jacob-jarick/esp-solar-contoller/docs/Solar Controller - Day Load.png

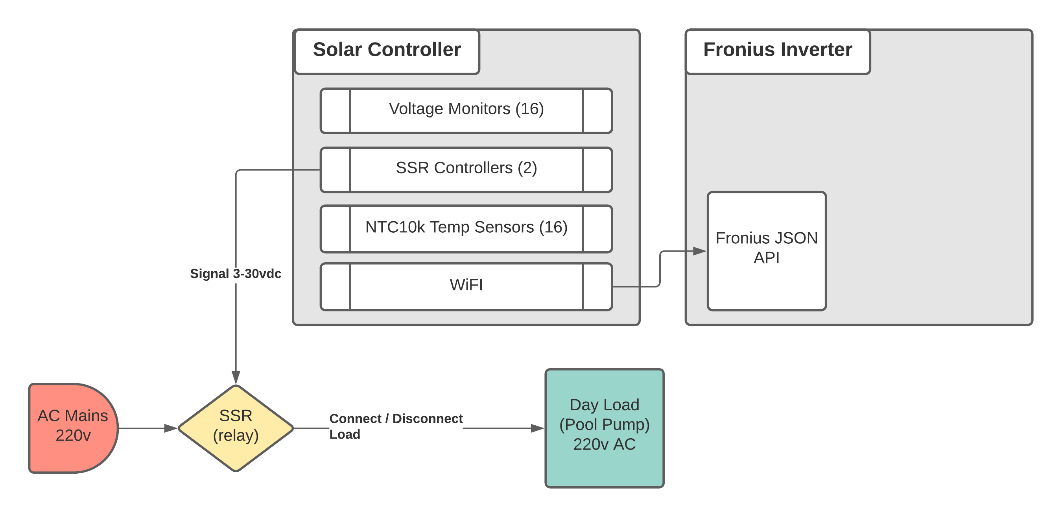
docs/Solar Controller - Day Load.png
