jacob-jarick/esp-solar-contoller/docs/Solar Controller - PowerWall.png

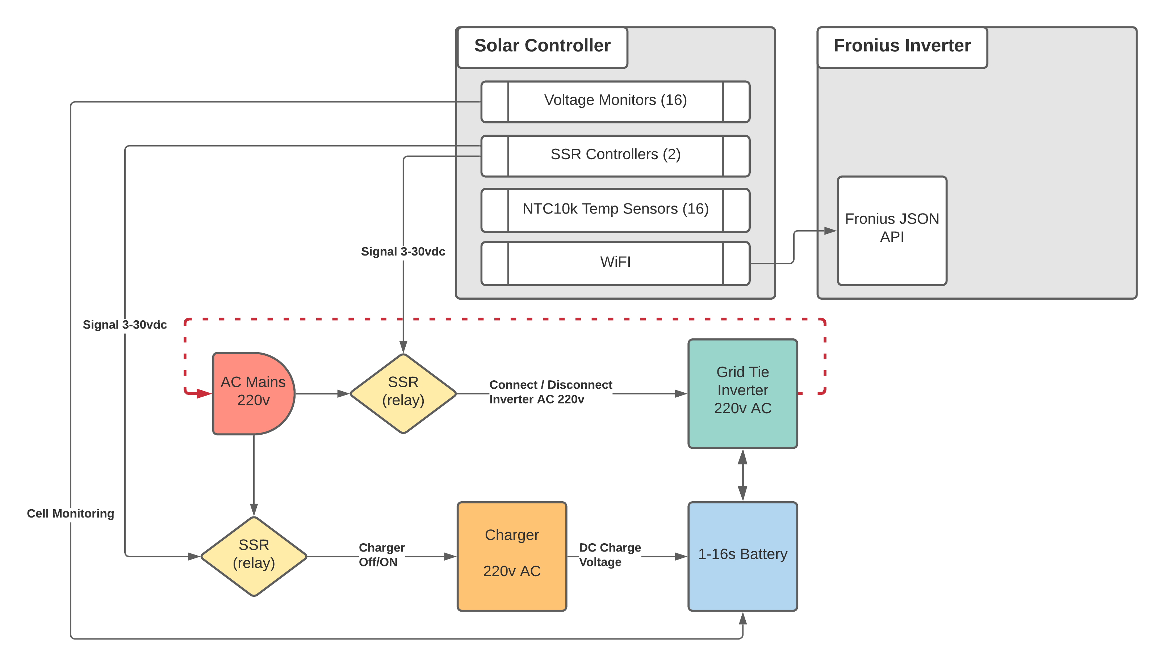
docs/Solar Controller - PowerWall.png
