jacob-jarick/esp-solar-contoller/pictures/advance menu.PNG

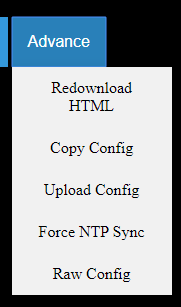
pictures/advance menu.PNG
