jacob-jarick/esp-solar-contoller/pictures/battery config.PNG

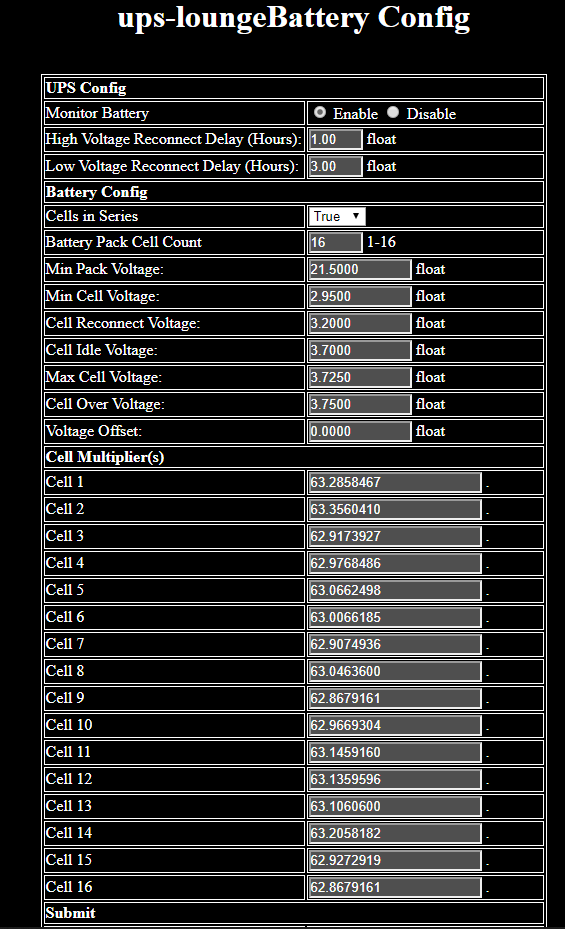
pictures/battery config.PNG
