jacob-jarick/esp-solar-contoller/pictures/battery info.PNG

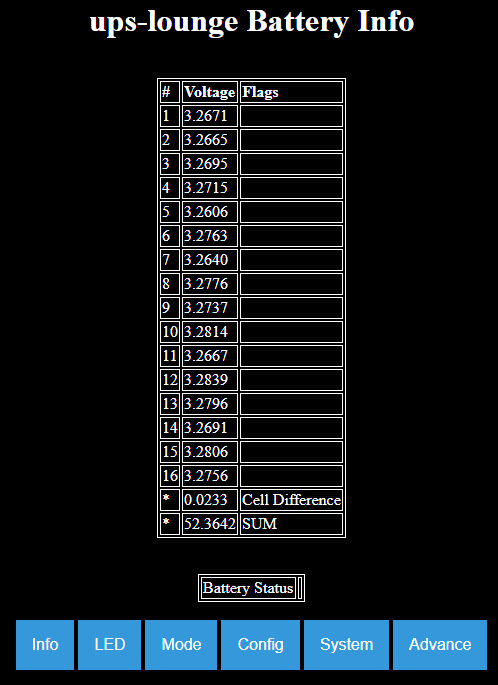
pictures/battery info.PNG
