jacob-jarick/esp-solar-contoller/pictures/config menu.PNG

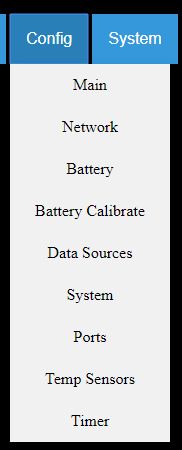
pictures/config menu.PNG
