jacob-jarick/esp-solar-contoller/pictures/info menu.PNG

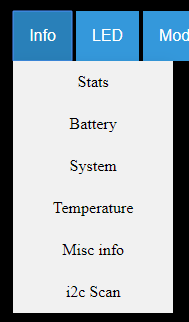
pictures/info menu.PNG
