jacob-jarick/esp-solar-contoller/pictures/led menu.PNG

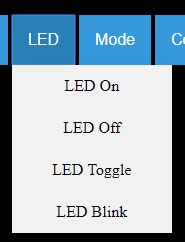
pictures/led menu.PNG
