jacob-jarick/esp-solar-contoller/pictures/main config.PNG

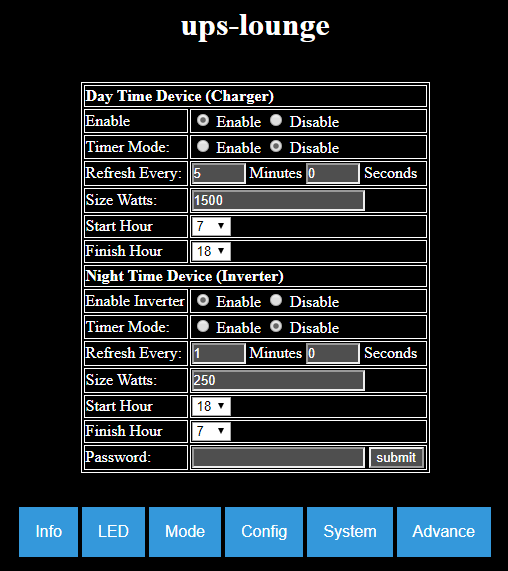
pictures/main config.PNG
