jacob-jarick/esp-solar-contoller/pictures/mode menu.PNG

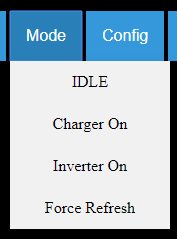
pictures/mode menu.PNG
