jacob-jarick/esp-solar-contoller/pictures/network config.PNG

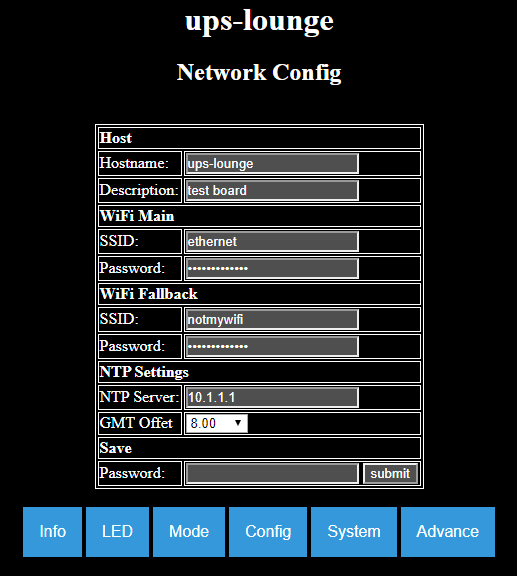
pictures/network config.PNG
