jacob-jarick/esp-solar-contoller/pictures/port config.PNG

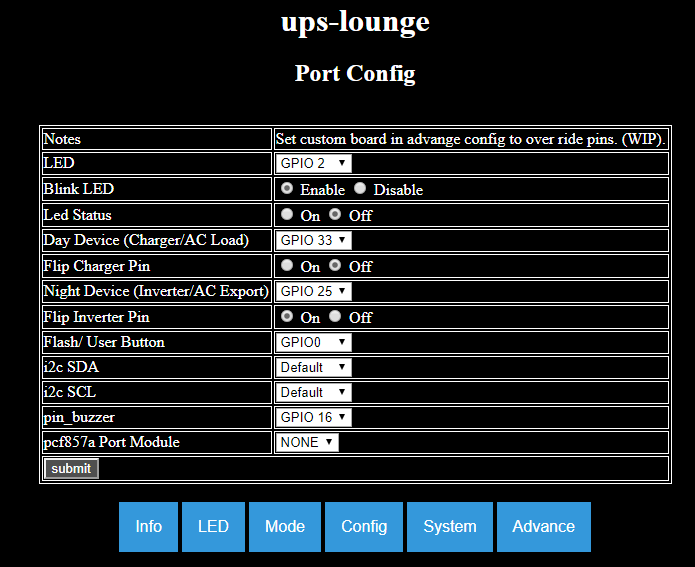
pictures/port config.PNG
