jacob-jarick/esp-solar-contoller/pictures/system info.PNG

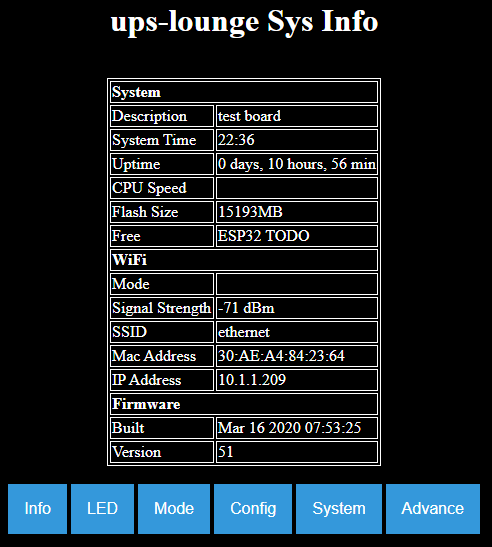
pictures/system info.PNG
