jacob-jarick/esp-solar-contoller/pictures/system menu.PNG

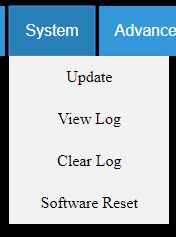
pictures/system menu.PNG
