jacob-jarick/esp-solar-contoller/pictures/temp config.PNG

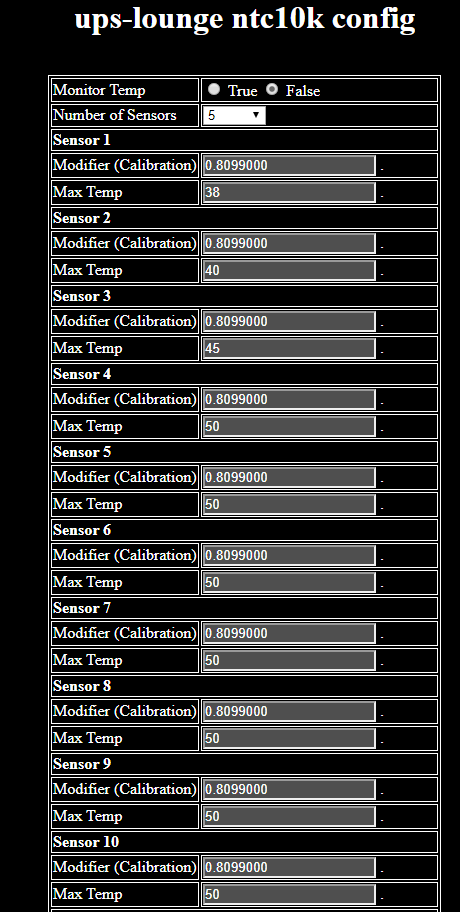
pictures/temp config.PNG
