jacob-jarick/esp-solar-contoller/pictures/battery calibrate.PNG

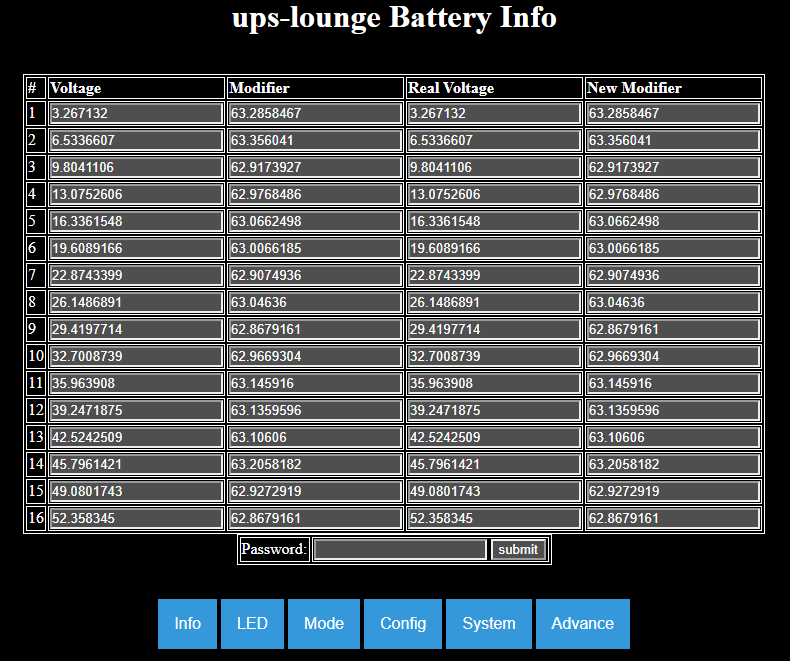
pictures/battery calibrate.PNG
