jacob-jarick/esp-solar-contoller/Arduino/esp32_solar_controller/fronius.ino

const uint8_t fronius_min_sync_seconds = 90;
unsigned long fronius_last_time = 0;

bool update_p_grid()
{
  bool fellback = 0;

  String payload;
  JsonDocument doc;

  String url = String(config.threephase_direct_url);

  // Direct URL
  if(timers.use_fallback < millis() && strlen(config.threephase_direct_url) )
  {
    bool check = get_url(url, payload);

    if(!check)
    {
      log_msg("Fronius Direct URL fetch Error");
      fellback = 1;
    }

    // decode json
    if(!fellback)
    {
      DeserializationError error2 = deserializeJson(doc, payload.c_str());

      if (error2)
      {
        log_msg(String("Fronius JSON Decode Error: ") + error2.c_str() );
        fellback = 1;
      }
    }
  }
  else
  {
    fellback = 1;
  }


  // attempt push URL
  if(fellback)
  {
    timers.use_fallback = millis() + (60 * 1000);

    if(!strlen(config.fronius_push_url))
      return 0;

    url = String(config.fronius_push_url);
    bool check = get_url(url, payload);

    if(!check)
    {
      log_msg("Fronius Fallback fetch Error");
      return 0;
    }

    DeserializationError error2 = deserializeJson(doc, payload.c_str());

    if (error2)
    {
      if(flags.fronius_error) // failed prior attempt, log message and clear flag
      {
        log_msg(String("Fronius Fallback JSON Decode Error: ") + error2.c_str() );
        flags.fronius_error = 0;
      }
      else
      {
        flags.fronius_error = 1; // set error flag, if happens next time log message
      }
      return 0;
    }
  }
  flags.fronius_error = 0; // clear error flag as no error found

  JsonObject root = doc.as<JsonObject>();
  JsonObject Body_0;

  // --------------------------------------------------------------------------
  // check time on JSON and compare to local time.

  if(fellback)
  {
    String tmp = root["Head"]["Timestamp"];

    unsigned long local_s = local_secs();
    unsigned long json_secs = fronius_time_str_to_secs(tmp);
    unsigned long time_diff = mmaths.mdiff<unsigned long>(json_secs, local_s);

    if (time_diff > fronius_min_sync_seconds)
    {
      log_msg("fronius: json time " + String(time_diff) + "+ seconds out of sync");
      return 0;
    }
  }

  // check and update fronius_last_time
  {
    String tmp = root["Head"]["Timestamp"];

    unsigned long json_secs = fronius_time_str_to_secs(tmp);

    // dont proceed if json files time is same as last check
    if(json_secs <= fronius_last_time)
      return 0;

    fronius_last_time = json_secs;
  }

  // --------------------------------------------------------------------------
  // get phase abc values from JSON

  if(fellback)
    Body_0 = root["Body"]["0"]; // push URL
  else
    Body_0 = root["Body"]["Data"]["0"]; // fetch (direct) url

  phase_a_watts = Body_0["PowerReal_P_Phase_1"];
  phase_b_watts = Body_0["PowerReal_P_Phase_2"];
  phase_c_watts = Body_0["PowerReal_P_Phase_3"];

  phase_a_voltage = Body_0["Voltage_AC_Phase_1"];
  phase_b_voltage = Body_0["Voltage_AC_Phase_2"];
  phase_c_voltage = Body_0["Voltage_AC_Phase_3"];

  phase_a_voltage_high = mmaths.mmax<float>(phase_a_voltage, phase_a_voltage_high);
  phase_b_voltage_high = mmaths.mmax<float>(phase_b_voltage, phase_b_voltage_high);
  phase_c_voltage_high = mmaths.mmax<float>(phase_c_voltage, phase_c_voltage_high);

  // check if voltage is greater than 0. we dont want min to be when grid is offline (ie 0)
  if(phase_a_voltage > 0)
    phase_a_voltage_low = mmaths.mmin<float>(phase_a_voltage, phase_a_voltage_low);

  if(phase_b_voltage > 0)
    phase_b_voltage_low = mmaths.mmin<float>(phase_b_voltage, phase_b_voltage_low);

  if(phase_c_voltage > 0)
  phase_c_voltage_low = mmaths.mmin<float>(phase_c_voltage, phase_c_voltage_low);

  if(!inverter_synced)
    inverter_synced = 1;

  timers.pgrid_last_update = millis();

  set_power(get_watts(1));

  return 1;
}


int8_t ceu_day = -1; // calc energy usage day
void calc_energy_usage()
{
  // calculate actual usage here
  // track energy consumed
  if(timers.calc_energy_usage != 0 && timeStatus() == timeNotSet )
  {
    float tmp_phase_sum = get_watts(3);

    float tmp_ms = millis() - timers.calc_energy_usage;

    energy_consumed += tmp_phase_sum * tmp_ms / 3600000.0 / 1000; // simplified maths, should catch decimals better too.

    int8_t tmp_day = day(now());

    if(ceu_day != tmp_day) // reset at midnight
    {
      ceu_day = tmp_day;
      energy_consumed_old = energy_consumed;
      energy_consumed = 0;
    }
  }

  timers.calc_energy_usage = millis();
}

// 0 = all summed
// 1 = only monitored
// 2 = only monitored and only if above 0
// 3 = ALL and only if above 0
float get_watts(uint8_t type)
{
  if(!config.threephase)
  {
    if(type == 0)
      return phase_a_watts;

    if(type == 1)
      return phase_a_watts;

    if(type == 3)
    {
      if(phase_a_watts > 0)
        return phase_a_watts;
      else
        return 0;
    }
  }

  float tmp = 0;

  if(type == 0)
  {
    tmp += phase_a_watts;
    tmp += phase_b_watts;
    tmp += phase_c_watts;

    return tmp;
  }
  if(type == 1)
  {
    if(config.monitor_phase_a)
      tmp += phase_a_watts;
    if(config.monitor_phase_b)
      tmp += phase_b_watts;
    if(config.monitor_phase_c)
      tmp += phase_c_watts;

    return tmp;
  }

  if(type == 2)
  {
    if(config.monitor_phase_a && phase_a_watts > 0)
      tmp += phase_a_watts;
    if(config.monitor_phase_b && phase_b_watts > 0)
      tmp += phase_b_watts;
    if(config.monitor_phase_c && phase_b_watts > 0)
      tmp += phase_c_watts;

    return tmp;
  }

  if(type == 3)
  {
    if(phase_a_watts > 0)
      tmp += phase_a_watts;
    if(phase_b_watts > 0)
      tmp += phase_b_watts;
    if(phase_c_watts > 0)
      tmp += phase_c_watts;

    return tmp;
  }

  return -1;
}

float power_array[power_array_size];
int8_t power_array_pos = -1;

void set_power(const float p)
{
  if(config.avg_phase <= 1 || config.api_grid)
  {
    phase_sum = p;
    return;
  }

  // -----------------------------------------------
  // begin average code

  // populate array on first use
  if(power_array_pos == -1)
  {
    for(uint8_t i = 0; i < power_array_size; i++)
      power_array[i] = p;
  }
  else
  {
    power_array[power_array_pos] = p;
  }

  power_array_pos++;
  if(power_array_pos >= power_array_size || power_array_pos >= config.avg_phase)
    power_array_pos = 0;

  phase_avg = 0;
  for(uint8_t i = 0; i < config.avg_phase; i++)
    phase_avg += power_array[i];

  phase_avg = phase_avg / config.avg_phase;

  phase_sum = phase_avg;
}

unsigned long fronius_time_str_to_secs(String tmp)
{
  uint16_t json_y = tmp.substring(0, 4).toInt();
  uint8_t json_month = tmp.substring(5, 7).toInt();
  uint8_t json_d = tmp.substring(8, 10).toInt();

  uint8_t json_h = tmp.substring(11, 13).toInt();
  uint8_t json_min = tmp.substring(14, 16).toInt();
  uint8_t json_s = tmp.substring(17, 19).toInt();

//   Serial.println("\nF:" + String(json_y) + "." + String(json_month) + "." +  String(json_d) + "-" +  String(json_h) + ":" + String(json_min) + ":" + String(json_s) + "\n");

  return mmaths.ymdhms_to_sec(json_y, json_month, json_d, json_h, json_min, json_s);
}



unsigned long local_secs()
{
  time_t timetmp = now();
//   Serial.println("\nL " + String(year(timetmp)) + "-" + String(month(timetmp)) + "-" + String(day(timetmp)) + "-" + String(hour(timetmp)) + "-" + String(minute(timetmp)) + "-" + String(second(timetmp)) + "\n");
  return mmaths.ymdhms_to_sec(year(timetmp), month(timetmp), day(timetmp), hour(timetmp), minute(timetmp), second(timetmp));
}
