jacob-jarick/esp-solar-contoller/Arduino/esp32_solar_controller/beep.ino

void beep_helper(const uint16_t freq, const uint16_t tdelay)
{
  Serial.println("pin: " + String(pin_buzzer) + ", Freq: " + String(freq));

  // uint32_t ledcWriteTone(uint8_t pin, uint32_t freq);
  ledcWriteTone(pin_buzzer, freq);
  delay(tdelay);
  ledcWriteTone(pin_buzzer, 0);
}
